nfield0/DMNAlarms/indoor.py

import RPi.GPIO as GPIO
import time, threading

from pubnub.callbacks import SubscribeCallback
from pubnub.enums import PNStatusCategory, PNOperationType
from pubnub.pnconfiguration import PNConfiguration
from pubnub.pubnub import PubNub

# Switch Function
# Detect switch inputs

# Buzzer


# Door Sensing
# Log when door is closed and door is opened
